harshitgoel96/Ergodox_BLE/ErgodoxBle Case/all_combined.png

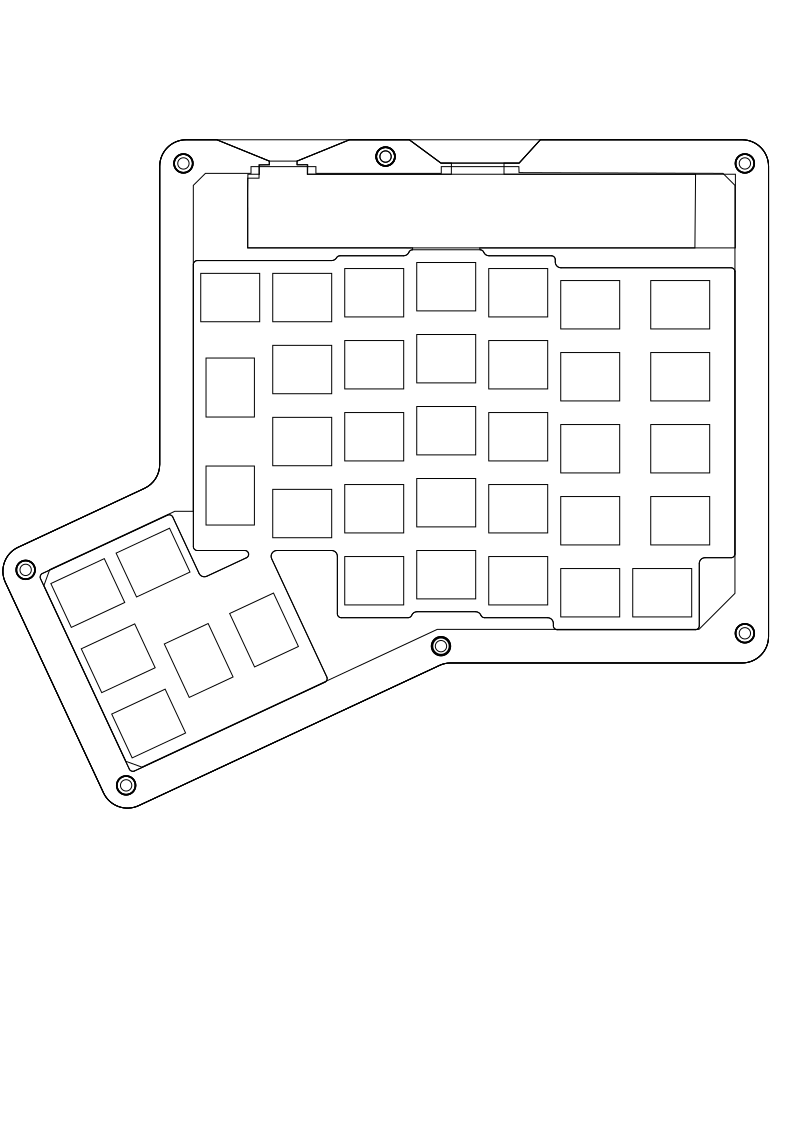
ErgodoxBle Case/all_combined.png
